LennyGodart/THE-WALL/docs/images/panel-notes.de.png

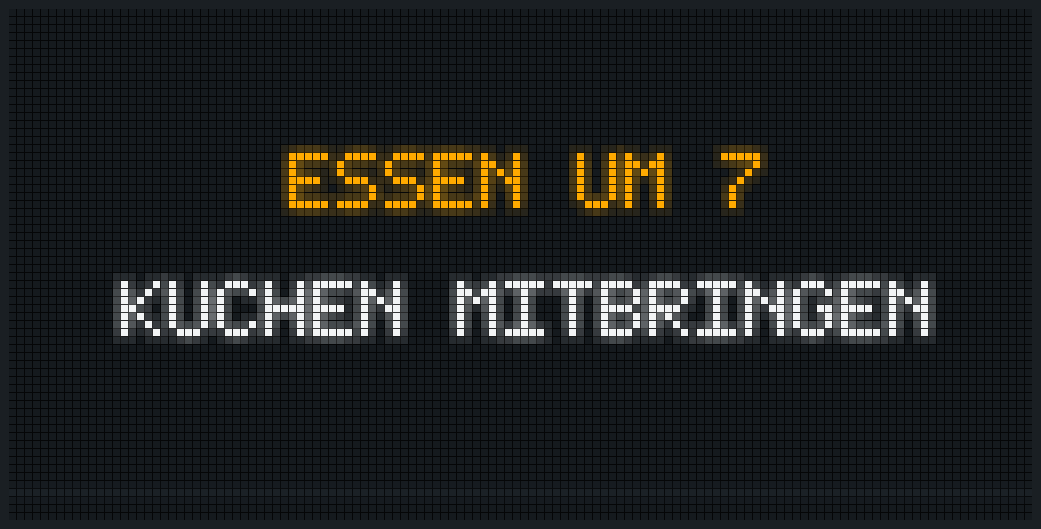
docs/images/panel-notes.de.png
