LennyGodart/THE-WALL/docs/images/site-device.de.png

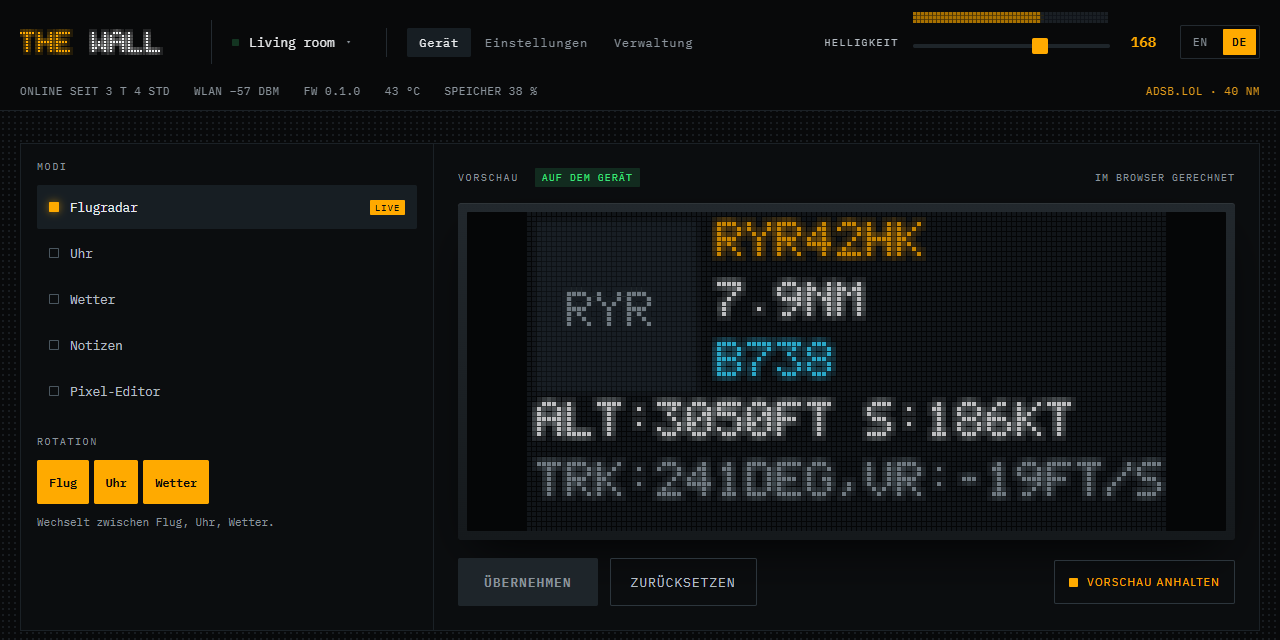
docs/images/site-device.de.png
