LennyGodart/THE-WALL/docs/images/site-flight.de.png

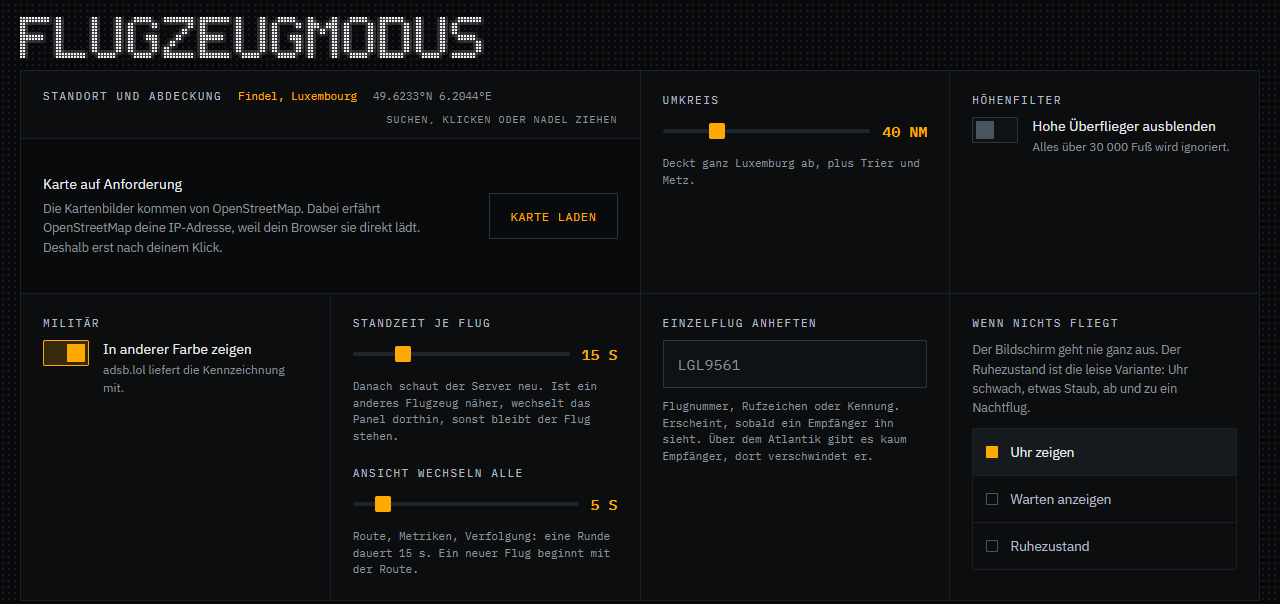
docs/images/site-flight.de.png
