LennyGodart/THE-WALL/firmware/src/certs.h

// Erzeugt von tools/certs.mjs, nicht von Hand aendern. Stammzertifikate fuer den Server.
#pragma once

static const char ROOT_CERTS[] =
// GTS Root R1
"-----BEGIN CERTIFICATE-----\n"
"MIIFVzCCAz+gAwIBAgINAgPlk28xsBNJiGuiFzANBgkqhkiG9w0BAQwFADBHMQsw\n"
"CQYDVQQGEwJVUzEiMCAGA1UEChMZR29vZ2xlIFRydXN0IFNlcnZpY2VzIExMQzEU\n"
"MBIGA1UEAxMLR1RTIFJvb3QgUjEwHhcNMTYwNjIyMDAwMDAwWhcNMzYwNjIyMDAw\n"
"MDAwWjBHMQswCQYDVQQGEwJVUzEiMCAGA1UEChMZR29vZ2xlIFRydXN0IFNlcnZp\n"
"Y2VzIExMQzEUMBIGA1UEAxMLR1RTIFJvb3QgUjEwggIiMA0GCSqGSIb3DQEBAQUA\n"
"A4ICDwAwggIKAoICAQC2EQKLHuOhd5s73L+UPreVp0A8of2C+X0yBoJx9vaMf/vo\n"
"27xqLpeXo4xL+Sv2sfnOhB2x+cWX3u+58qPpvBKJXqeqUqv4IyfLpLGcY9vXmX7w\n"
"Cl7raKb0xlpHDU0QM+NOsROjyBhsS+z8CZDfnWQpJSMHobTSPS5g4M/SCYe7zUjw\n"
"TcLCeoiKu7rPWRnWr4+wB7CeMfGCwcDfLqZtbBkOtdh+JhpFAz2weaSUKK0Pfybl\n"
"qAj+lug8aJRT7oM6iCsVlgmy4HqMLnXWnOunVmSPlk9orj2XwoSPwLxAwAtcvfaH\n"
"szVsrBhQf4TgTM2S0yDpM7xSma8ytSmzJSq0SPly4cpk9+aCEI3oncKKiPo4Zor8\n"
"Y/kB+Xj9e1x3+naH+uzfsQ55lVe0vSbv1gHR6xYKu44LtcXFilWr06zqkUspzBmk\n"
"MiVOKvFlRNACzqrOSbTqn3yDsEB750Orp2yjj32JgfpMpf/VjsPOS+C12LOORc92\n"
"wO1AK/1TD7Cn1TsNsYqiA94xrcx36m97PtbfkSIS5r762DL8EGMUUXLeXdYWk70p\n"
"aDPvOmbsB4om3xPXV2V4J95eSRQAogB/mqghtqmxlbCluQ0WEdrHbEg8QOB+DVrN\n"
"VjzRlwW5y0vtOUucxD/SVRNuJLDWcfr0wbrM7Rv1/oFB2ACYPTrIrnqYNxgFlQID\n"
"AQABo0IwQDAOBgNVHQ8BAf8EBAMCAYYwDwYDVR0TAQH/BAUwAwEB/zAdBgNVHQ4E\n"
"FgQU5K8rJnEaK0gnhS9SZizv8IkTcT4wDQYJKoZIhvcNAQEMBQADggIBAJ+qQibb\n"
"C5u+/x6Wki4+omVKapi6Ist9wTrYggoGxval3sBOh2Z5ofmmWJyq+bXmYOfg6LEe\n"
"QkEzCzc9zolwFcq1JKjPa7XSQCGYzyI0zzvFIoTgxQ6KfF2I5DUkzps+GlQebtuy\n"
"h6f88/qBVRRiClmpIgUxPoLW7ttXNLwzldMXG+gnoot7TiYaelpkttGsN/H9oPM4\n"
"7HLwEXWdyzRSjeZ2axfG34arJ45JK3VmgRAhpuo+9K4l/3wV3s6MJT/KYnAK9y8J\n"
"ZgfIPxz88NtFMN9iiMG1D53Dn0reWVlHxYciNuaCp+0KueIHoI17eko8cdLiA6Ef\n"
"MgfdG+RCzgwARWGAtQsgWSl4vflVy2PFPEz0tv/bal8xa5meLMFrUKTX5hgUvYU/\n"
"Z6tGn6D/Qqc6f1zLXbBwHSs09dR2CQzreExZBfMzQsNhFRAbd03OIozUhfJFfbdT\n"
"6u9AWpQKXCBfTkBdYiJ23//OYb2MI3jSNwLgjt7RETeJ9r/tSQdirpLsQBqvFAnZ\n"
"0E6yove+7u7Y/9waLd64NnHi/Hm3lCXRSHNboTXns5lndcEZOitHTtNCjv0xyBZm\n"
"2tIMPNuzjsmhDYAPexZ3FL//2wmUspO8IFgV6dtxQ/PeEMMA3KgqlbbC1j+Qa3bb\n"
"bP6MvPJwNQzcmRk13NfIRmPVNnGuV/u3gm3c\n"
"-----END CERTIFICATE-----\n"
// GTS Root R3
"-----BEGIN CERTIFICATE-----\n"
"MIICCTCCAY6gAwIBAgINAgPluILrIPglJ209ZjAKBggqhkjOPQQDAzBHMQswCQYD\n"
"VQQGEwJVUzEiMCAGA1UEChMZR29vZ2xlIFRydXN0IFNlcnZpY2VzIExMQzEUMBIG\n"
"A1UEAxMLR1RTIFJvb3QgUjMwHhcNMTYwNjIyMDAwMDAwWhcNMzYwNjIyMDAwMDAw\n"
"WjBHMQswCQYDVQQGEwJVUzEiMCAGA1UEChMZR29vZ2xlIFRydXN0IFNlcnZpY2Vz\n"
"IExMQzEUMBIGA1UEAxMLR1RTIFJvb3QgUjMwdjAQBgcqhkjOPQIBBgUrgQQAIgNi\n"
"AAQfTzOHMymKoYTey8chWEGJ6ladK0uFxh1MJ7x/JlFyb+Kf1qPKzEUURout736G\n"
"jOyxfi//qXGdGIRFBEFVbivqJn+7kAHjSxm65FSWRQmx1WyRRK2EE46ajA2ADDL2\n"
"4CejQjBAMA4GA1UdDwEB/wQEAwIBhjAPBgNVHRMBAf8EBTADAQH/MB0GA1UdDgQW\n"
"BBTB8Sa6oC2uhYHP0/EqEr24Cmf9vDAKBggqhkjOPQQDAwNpADBmAjEA9uEglRR7\n"
"VKOQFhG/hMjqb2sXnh5GmCCbn9MN2azTL818+FsuVbu/3ZL3pAzcMeGiAjEA/Jdm\n"
"ZuVDFhOD3cffL74UOO0BzrEXGhF16b0DjyZ+hOXJYKaV11RZt+cRLInUue4X\n"
"-----END CERTIFICATE-----\n"
// GTS Root R4
"-----BEGIN CERTIFICATE-----\n"
"MIICCTCCAY6gAwIBAgINAgPlwGjvYxqccpBQUjAKBggqhkjOPQQDAzBHMQswCQYD\n"
"VQQGEwJVUzEiMCAGA1UEChMZR29vZ2xlIFRydXN0IFNlcnZpY2VzIExMQzEUMBIG\n"
"A1UEAxMLR1RTIFJvb3QgUjQwHhcNMTYwNjIyMDAwMDAwWhcNMzYwNjIyMDAwMDAw\n"
"WjBHMQswCQYDVQQGEwJVUzEiMCAGA1UEChMZR29vZ2xlIFRydXN0IFNlcnZpY2Vz\n"
"IExMQzEUMBIGA1UEAxMLR1RTIFJvb3QgUjQwdjAQBgcqhkjOPQIBBgUrgQQAIgNi\n"
"AATzdHOnaItgrkO4NcWBMHtLSZ37wWHO5t5GvWvVYRg1rkDdc/eJkTBa6zzuhXyi\n"
"QHY7qca4R9gq55KRanPpsXI5nymfopjTX15YhmUPoYRlBtHci8nHc8iMai/lxKvR\n"
"HYqjQjBAMA4GA1UdDwEB/wQEAwIBhjAPBgNVHRMBAf8EBTADAQH/MB0GA1UdDgQW\n"
"BBSATNbrdP9JNqPV2Py1PsVq8JQdjDAKBggqhkjOPQQDAwNpADBmAjEA6ED/g94D\n"
"9J+uHXqnLrmvT/aDHQ4thQEd0dlq7A/Cr8deVl5c1RxYIigL9zC2L7F8AjEA8GE8\n"
"p/SgguMh1YQdc4acLa/KNJvxn7kjNuK8YAOdgLOaVsjh4rsUecrNIdSUtUlD\n"
"-----END CERTIFICATE-----\n"
// ISRG Root X1
"-----BEGIN CERTIFICATE-----\n"
"MIIFazCCA1OgAwIBAgIRAIIQz7DSQONZRGPgu2OCiwAwDQYJKoZIhvcNAQELBQAw\n"
"TzELMAkGA1UEBhMCVVMxKTAnBgNVBAoTIEludGVybmV0IFNlY3VyaXR5IFJlc2Vh\n"
"cmNoIEdyb3VwMRUwEwYDVQQDEwxJU1JHIFJvb3QgWDEwHhcNMTUwNjA0MTEwNDM4\n"
"WhcNMzUwNjA0MTEwNDM4WjBPMQswCQYDVQQGEwJVUzEpMCcGA1UEChMgSW50ZXJu\n"
"ZXQgU2VjdXJpdHkgUmVzZWFyY2ggR3JvdXAxFTATBgNVBAMTDElTUkcgUm9vdCBY\n"
"MTCCAiIwDQYJKoZIhvcNAQEBBQADggIPADCCAgoCggIBAK3oJHP0FDfzm54rVygc\n"
"h77ct984kIxuPOZXoHj3dcKi/vVqbvYATyjb3miGbESTtrFj/RQSa78f0uoxmyF+\n"
"0TM8ukj13Xnfs7j/EvEhmkvBioZxaUpmZmyPfjxwv60pIgbz5MDmgK7iS4+3mX6U\n"
"A5/TR5d8mUgjU+g4rk8Kb4Mu0UlXjIB0ttov0DiNewNwIRt18jA8+o+u3dpjq+sW\n"
"T8KOEUt+zwvo/7V3LvSye0rgTBIlDHCNAymg4VMk7BPZ7hm/ELNKjD+Jo2FR3qyH\n"
"B5T0Y3HsLuJvW5iB4YlcNHlsdu87kGJ55tukmi8mxdAQ4Q7e2RCOFvu396j3x+UC\n"
"B5iPNgiV5+I3lg02dZ77DnKxHZu8A/lJBdiB3QW0KtZB6awBdpUKD9jf1b0SHzUv\n"
"KBds0pjBqAlkd25HN7rOrFleaJ1/ctaJxQZBKT5ZPt0m9STJEadao0xAH0ahmbWn\n"
"OlFuhjuefXKnEgV4We0+UXgVCwOPjdAvBbI+e0ocS3MFEvzG6uBQE3xDk3SzynTn\n"
"jh8BCNAw1FtxNrQHusEwMFxIt4I7mKZ9YIqioymCzLq9gwQbooMDQaHWBfEbwrbw\n"
"qHyGO0aoSCqI3Haadr8faqU9GY/rOPNk3sgrDQoo//fb4hVC1CLQJ13hef4Y53CI\n"
"rU7m2Ys6xt0nUW7/vGT1M0NPAgMBAAGjQjBAMA4GA1UdDwEB/wQEAwIBBjAPBgNV\n"
"HRMBAf8EBTADAQH/MB0GA1UdDgQWBBR5tFnme7bl5AFzgAiIyBpY9umbbjANBgkq\n"
"hkiG9w0BAQsFAAOCAgEAVR9YqbyyqFDQDLHYGmkgJykIrGF1XIpu+ILlaS/V9lZL\n"
"ubhzEFnTIZd+50xx+7LSYK05qAvqFyFWhfFQDlnrzuBZ6brJFe+GnY+EgPbk6ZGQ\n"
"3BebYhtF8GaV0nxvwuo77x/Py9auJ/GpsMiu/X1+mvoiBOv/2X/qkSsisRcOj/KK\n"
"NFtY2PwByVS5uCbMiogziUwthDyC3+6WVwW6LLv3xLfHTjuCvjHIInNzktHCgKQ5\n"
"ORAzI4JMPJ+GslWYHb4phowim57iaztXOoJwTdwJx4nLCgdNbOhdjsnvzqvHu7Ur\n"
"TkXWStAmzOVyyghqpZXjFaH3pO3JLF+l+/+sKAIuvtd7u+Nxe5AW0wdeRlN8NwdC\n"
"jNPElpzVmbUq4JUagEiuTDkHzsxHpFKVK7q4+63SM1N95R1NbdWhscdCb+ZAJzVc\n"
"oyi3B43njTOQ5yOf+1CceWxG1bQVs5ZufpsMljq4Ui0/1lvh+wjChP4kqKOJ2qxq\n"
"4RgqsahDYVvTH9w7jXbyLeiNdd8XM2w9U/t7y0Ff/9yi0GE44Za4rF2LN9d11TPA\n"
"mRGunUHBcnWEvgJBQl9nJEiU0Zsnvgc/ubhPgXRR4Xq37Z0j4r7g1SgEEzwxA57d\n"
"emyPxgcYxn/eR44/KJ4EBs+lVDR3veyJm+kXQ99b21/+jh5Xos1AnX5iItreGCc=\n"
"-----END CERTIFICATE-----\n"
// ISRG Root X2
"-----BEGIN CERTIFICATE-----\n"
"MIICGzCCAaGgAwIBAgIQQdKd0XLq7qeAwSxs6S+HUjAKBggqhkjOPQQDAzBPMQsw\n"
"CQYDVQQGEwJVUzEpMCcGA1UEChMgSW50ZXJuZXQgU2VjdXJpdHkgUmVzZWFyY2gg\n"
"R3JvdXAxFTATBgNVBAMTDElTUkcgUm9vdCBYMjAeFw0yMDA5MDQwMDAwMDBaFw00\n"
"MDA5MTcxNjAwMDBaME8xCzAJBgNVBAYTAlVTMSkwJwYDVQQKEyBJbnRlcm5ldCBT\n"
"ZWN1cml0eSBSZXNlYXJjaCBHcm91cDEVMBMGA1UEAxMMSVNSRyBSb290IFgyMHYw\n"
"EAYHKoZIzj0CAQYFK4EEACIDYgAEzZvVn4CDCuwJSvMWSj5cz3es3mcFDR0HttwW\n"
"+1qLFNvicWDEukWVEYmO6gbf9yoWHKS5xcUy4APgHoIYOIvXRdgKam7mAHf7AlF9\n"
"ItgKbppbd9/w+kHsOdx1ymgHDB/qo0IwQDAOBgNVHQ8BAf8EBAMCAQYwDwYDVR0T\n"
"AQH/BAUwAwEB/zAdBgNVHQ4EFgQUfEKWrt5LSDv6kviejM9ti6lyN5UwCgYIKoZI\n"
"zj0EAwMDaAAwZQIwe3lORlCEwkSHRhtFcP9Ymd70/aTSVaYgLXTWNLxBo1BfASdW\n"
"tL4ndQavEi51mI38AjEAi/V3bNTIZargCyzuFJ0nN6T5U6VR5CmD1/iQMVtCnwr1\n"
"/q4AaOeMSQ+2b1tbFfLn\n"
"-----END CERTIFICATE-----\n"
// SSL.com TLS RSA Root CA 2022
"-----BEGIN CERTIFICATE-----\n"
"MIIFiTCCA3GgAwIBAgIQb77arXO9CEDii02+1PdbkTANBgkqhkiG9w0BAQsFADBO\n"
"MQswCQYDVQQGEwJVUzEYMBYGA1UECgwPU1NMIENvcnBvcmF0aW9uMSUwIwYDVQQD\n"
"DBxTU0wuY29tIFRMUyBSU0EgUm9vdCBDQSAyMDIyMB4XDTIyMDgyNTE2MzQyMloX\n"
"DTQ2MDgxOTE2MzQyMVowTjELMAkGA1UEBhMCVVMxGDAWBgNVBAoMD1NTTCBDb3Jw\n"
"b3JhdGlvbjElMCMGA1UEAwwcU1NMLmNvbSBUTFMgUlNBIFJvb3QgQ0EgMjAyMjCC\n"
"AiIwDQYJKoZIhvcNAQEBBQADggIPADCCAgoCggIBANCkCXJPQIgSYT41I57u9nTP\n"
"L3tYPc48DRAokC+X94xI2KDYJbFMsBFMF3NQ0CJKY7uB0ylu1bUJPiYYf7ISf5OY\n"
"t6/wNr/y7hienDtSxUcZXXTzZGbVXcdotL8bHAajvI9AI7YexoS9UcQbOcGV0ins\n"
"S657Lb85/bRi3pZ7QcacoOAGcvvwB5cJOYF0r/c0WRFXCsJbwST0MXMwgsadugL3\n"
"PnxEX4MN8/HdIGkWCVDi1FW24IBydm5MR7d1VVm0U3TZlMZBrViKMWYPHqIbKUBO\n"
"L9975hYsLfy/7PO0+r4Y9ptJ1O4Fbtk085zx7AGL0SDGD6C1vBdOSHtRwvzpXGk3\n"
"R2azaPgVKPC506QVzFpPulJwoxJF3ca6TvvC0PeoUidtbnm1jPx7jMEWTO6Af77w\n"
"dr5BUxIzrlo4QqvXDz5BjXYHMtWrifZOZ9mxQnUjbvPNQrL8VfVThxc7wDNY8VLS\n"
"+YCk8OjwO4s4zKTGkH8PnP2L0aPP2oOnaclQNtVcBdIKQXTbYxE3waWglksejBYS\n"
"d66UNHsef8JmAOSqg+qKkK3ONkRN0VHpvB/zagX9wHQfJRlAUW7qglFA35u5CCoG\n"
"AtUjHBPW6dvbxrB6y3snm/vg1UYk7RBLY0ulBY+6uB0rpvqR4pJSvezrZ5dtmi2f\n"
"gTIFZzL7SAg/2SW4BCUvAgMBAAGjYzBhMA8GA1UdEwEB/wQFMAMBAf8wHwYDVR0j\n"
"BBgwFoAU+y437uOEeicuzRk1sTN8/9REQrkwHQYDVR0OBBYEFPsuN+7jhHonLs0Z\n"
"NbEzfP/UREK5MA4GA1UdDwEB/wQEAwIBhjANBgkqhkiG9w0BAQsFAAOCAgEAjYlt\n"
"hEUY8U+zoO9opMAdrDC8Z2awms22qyIZZtM7QbUQnRC6cm4pJCAcAZli05bg4vsM\n"
"QtfhWsSWTVTNj8pDU/0quOr4ZcoBwq1gaAafORpR2eCNJvkLTqVTJXojpBzOCBvf\n"
"R4iyrT7gJ4eLSYwfqUdYe5byiB0YrrPRpgqU+tvT5TgKa3kSM/tKWTcWQA673vWJ\n"
"DPFs0/dRa1419dvAJuoSc06pkZCmF8NsLzjUo3KUQyxi4U5cMj29TH0ZR6LDSeeW\n"
"P4+a0zvkEdiLA9z2tmBVGKaBUfPhqBVq6+AL8BQx1rmMRTqoENjwuSfr98t67wVy\n"
"lrXEj5ZzxOhWc5y8aVFjvO9nHEMaX3cZHxj4HCUp+UmZKbaSPaKDN7EgkaibMOlq\n"
"bLQjk2UEqxHzDh1TJElTHaE/nUiSEeJ9DU/1172iWD54nR4fK/4huxoTtrEoZP2w\n"
"AgDHbICivRZQIA9ygV/MlP+7mea6kMvq+cYMwq7FGc4zoWtcu358NFcXrfA/rs3q\n"
"r5nsLFR+jM4uElZI7xc7P0peYNLcdDa8pUNjyw9bowJWCZ4kLOGGgYz+qxcs+sji\n"
"Mho6/4UIyYOf8kpIEFR3N+2ivEC+5BB09+Rbu7nzifmPQdjH5FCQNYA+HLhNkNPU\n"
"98OwoX6EyneSMSy4kLGCenROmxMmtNVQZlR4rmA=\n"
"-----END CERTIFICATE-----\n"
// SSL.com TLS ECC Root CA 2022
"-----BEGIN CERTIFICATE-----\n"
"MIICOjCCAcCgAwIBAgIQFAP1q/s3ixdAW+JDsqXRxDAKBggqhkjOPQQDAzBOMQsw\n"
"CQYDVQQGEwJVUzEYMBYGA1UECgwPU1NMIENvcnBvcmF0aW9uMSUwIwYDVQQDDBxT\n"
"U0wuY29tIFRMUyBFQ0MgUm9vdCBDQSAyMDIyMB4XDTIyMDgyNTE2MzM0OFoXDTQ2\n"
"MDgxOTE2MzM0N1owTjELMAkGA1UEBhMCVVMxGDAWBgNVBAoMD1NTTCBDb3Jwb3Jh\n"
"dGlvbjElMCMGA1UEAwwcU1NMLmNvbSBUTFMgRUNDIFJvb3QgQ0EgMjAyMjB2MBAG\n"
"ByqGSM49AgEGBSuBBAAiA2IABEUpNXP6wrgjzhR9qLFNoFs27iosU8NgCTWyJGYm\n"
"acCzldZdkkAZDsalE3D07xJRKF3nzL35PIXBz5SQySvOkkJYWWf9lCcQZIxPBLFN\n"
"SeR7T5v15wj4A4j3p8OSSxlUgaNjMGEwDwYDVR0TAQH/BAUwAwEB/zAfBgNVHSME\n"
"GDAWgBSJjy+j6CugFFR781a4Jl9nOAuc0DAdBgNVHQ4EFgQUiY8vo+groBRUe/NW\n"
"uCZfZzgLnNAwDgYDVR0PAQH/BAQDAgGGMAoGCCqGSM49BAMDA2gAMGUCMFXjIlbp\n"
"15IkWE8elDIPDAI2wv2sdDJO4fscgIijzPvX6yv/N33w7deedWo1dlJF4AIxAMeN\n"
"b0Igj762TVntd00pxCAgRWSGOlDGxK0tk/UYfXLtqc/ErFc2KAhl3zx5Zn6g6g==\n"
"-----END CERTIFICATE-----\n"
// SSL.com Root Certification Authority RSA
"-----BEGIN CERTIFICATE-----\n"
"MIIF3TCCA8WgAwIBAgIIeyyb0xaAMpkwDQYJKoZIhvcNAQELBQAwfDELMAkGA1UE\n"
"BhMCVVMxDjAMBgNVBAgMBVRleGFzMRAwDgYDVQQHDAdIb3VzdG9uMRgwFgYDVQQK\n"
"DA9TU0wgQ29ycG9yYXRpb24xMTAvBgNVBAMMKFNTTC5jb20gUm9vdCBDZXJ0aWZp\n"
"Y2F0aW9uIEF1dGhvcml0eSBSU0EwHhcNMTYwMjEyMTczOTM5WhcNNDEwMjEyMTcz\n"
"OTM5WjB8MQswCQYDVQQGEwJVUzEOMAwGA1UECAwFVGV4YXMxEDAOBgNVBAcMB0hv\n"
"dXN0b24xGDAWBgNVBAoMD1NTTCBDb3Jwb3JhdGlvbjExMC8GA1UEAwwoU1NMLmNv\n"
"bSBSb290IENlcnRpZmljYXRpb24gQXV0aG9yaXR5IFJTQTCCAiIwDQYJKoZIhvcN\n"
"AQEBBQADggIPADCCAgoCggIBAPkP3aMrfcvQKv7sZ4Wm5y4bunfh4/WvpOz6Sl2R\n"
"xFdHaxh3a3by/ZPkPQ/CFp4LZsNWlJ4Xg4XOVu/yFv0AYvUiCVToZRdOQbngT0aX\n"
"qhvIuG5iXmmxX9sqAn78bMrzQdjt0Oj8P2FI7bADFB0QDksZ4LtO7IZl/zbzXmcC\n"
"C52GVWH9ejjt/uIZALdvoVBidXQ8oPrIJZK0bnoix/geoeOy3ZExqysdBP+lSgQ3\n"
"6YWkMyv94tZVNHwZpEpox7Ko07fKoZOI68GXvIz5HdkihCR0xwQ9aqkpk8zruFvh\n"
"/l8lqjRYyMEjVJ0bmBHDOJx+PYZspQ9AhnwC9FwCTyjLrnGfDzrIM/4RJTXq/LrF\n"
"YD3ZfBjVsqnTdXgDciLKOsMf7yzlLqn6niy2UUb9rwPW6mBo6oUWNmuF6R7As93E\n"
"JNyAKoFBbZQ+yODJgUEAnl6/f8UImKIYLEJAs/lvOCdLToD0PYFH4Ih86hzOtXVc\n"
"US4cK38acijnALXRdMbX5J+tB5O2UzU1/Dfkw/ZdFr4hc96SCvigY2q8lpJqPvi8\n"
"ZVWb3vUNiSYE/CUapiVpy8JtynziWV+XrOvvLsi81xtZPCvM8hnIk2snYxnP/Okm\n"
"+Mpxm3+T/jRnhE6Z6/yzeAkzcLpmpnbtG3PrGqUNxCITIJRWCk4sbE6x/c+cCbqi\n"
"M+2HAgMBAAGjYzBhMB0GA1UdDgQWBBTdBAkHovV6fVJTEpKV7jiAJQ2mWTAPBgNV\n"
"HRMBAf8EBTADAQH/MB8GA1UdIwQYMBaAFN0ECQei9Xp9UlMSkpXuOIAlDaZZMA4G\n"
"A1UdDwEB/wQEAwIBhjANBgkqhkiG9w0BAQsFAAOCAgEAIBgRlCn7Jp0cHh5wYfGV\n"
"cpNxJK1ok1iOMq8bs3AD/CUrdIWQPXhq9LmLpZc7tRiRux6n+UBbkflVma8eEdBc\n"
"Hadm47GUBwwyOabqG7B52B2ccETjit3E+ZUfijhDPwGFpUenPUayvOUiaPd7nNgs\n"
"PgohyC0zrL/FgZkxdMF1ccW+sfAjRfSda/wZY52jvATGGAslu1OJD7OAUN5F7kR/\n"
"q5R4ZJjT9ijdh9hwZXT7DrkT66cPYakylszeu+1jTBi7qUD3oFRuIIhxdRjqerQ0\n"
"cuAjJ3dctpDqhiVAq+8zD8ufgr6iIPv2tS0a5sKFsXQP+8hlAqRSAUfdSSLBv9jr\n"
"a6x+3uxjMxW3IwiPxg+NQVrdjsW5j+VFP3jbutIbQLH+cU0/4IGiul607BXgk90I\n"
"H37hVZkLId6Tngr75qNJvTYw/ud3sqB1l7UtgYgXZSD32pAAn8lSzDLKNXz1PQ/Y\n"
"K9f1JmzJBjSWFupwWRoyeXkLtoh/D1JIPb9s2KJELtFOt3JY04kTlf5Eq/jXixtu\n"
"nLwsoFvVagCvXzfh1foQC5ichucmj87w7G6KVwuA406ywKBjYZC6VWg3dGq2ktuf\n"
"oYYitmUnDuy2n0Jg5GfCtdpBC8TTi2EbvPofkSvXRAdeuims2cXp71NIWuuA8ShY\n"
"Ic2wBlX7Jz9TkHCpBB5XJ7k=\n"
"-----END CERTIFICATE-----\n"
// SSL.com Root Certification Authority ECC
"-----BEGIN CERTIFICATE-----\n"
"MIICjTCCAhSgAwIBAgIIdebfy8FoW6gwCgYIKoZIzj0EAwIwfDELMAkGA1UEBhMC\n"
"VVMxDjAMBgNVBAgMBVRleGFzMRAwDgYDVQQHDAdIb3VzdG9uMRgwFgYDVQQKDA9T\n"
"U0wgQ29ycG9yYXRpb24xMTAvBgNVBAMMKFNTTC5jb20gUm9vdCBDZXJ0aWZpY2F0\n"
"aW9uIEF1dGhvcml0eSBFQ0MwHhcNMTYwMjEyMTgxNDAzWhcNNDEwMjEyMTgxNDAz\n"
"WjB8MQswCQYDVQQGEwJVUzEOMAwGA1UECAwFVGV4YXMxEDAOBgNVBAcMB0hvdXN0\n"
"b24xGDAWBgNVBAoMD1NTTCBDb3Jwb3JhdGlvbjExMC8GA1UEAwwoU1NMLmNvbSBS\n"
"b290IENlcnRpZmljYXRpb24gQXV0aG9yaXR5IEVDQzB2MBAGByqGSM49AgEGBSuB\n"
"BAAiA2IABEVuqVDEpiM2nl8ojRfLliJkP9x6jh3MCLOicSS6jkm5BBtHllirLZXI\n"
"7Z4INcgn64mMU1jrYor+8FsPazFSY0E7ic3s7LaNGdM0B9y7xgZ/wkWV7Mt/qCPg\n"
"CemB+vNH06NjMGEwHQYDVR0OBBYEFILRhXMw5zUE044CkvvlpNHEIejNMA8GA1Ud\n"
"EwEB/wQFMAMBAf8wHwYDVR0jBBgwFoAUgtGFczDnNQTTjgKS++Wk0cQh6M0wDgYD\n"
"VR0PAQH/BAQDAgGGMAoGCCqGSM49BAMCA2cAMGQCMG/n61kRpGDPYbCWe+0F+S8T\n"
"kdzt5fxQaxFGRrMcIQBiu77D5+jNB5n5DQtdcj7EqgIwH7y6C+IwJPt8bYBVCpk+\n"
"gA0z5Wajs6O7pdWLjwkspl1+4vAHCGht0nxpbl/f5Wpl\n"
"-----END CERTIFICATE-----\n"
// GlobalSign Root R46
"-----BEGIN CERTIFICATE-----\n"
"MIIFWjCCA0KgAwIBAgISEdK7udcjGJ5AXwqdLdDfJWfRMA0GCSqGSIb3DQEBDAUA\n"
"MEYxCzAJBgNVBAYTAkJFMRkwFwYDVQQKExBHbG9iYWxTaWduIG52LXNhMRwwGgYD\n"
"VQQDExNHbG9iYWxTaWduIFJvb3QgUjQ2MB4XDTE5MDMyMDAwMDAwMFoXDTQ2MDMy\n"
"MDAwMDAwMFowRjELMAkGA1UEBhMCQkUxGTAXBgNVBAoTEEdsb2JhbFNpZ24gbnYt\n"
"c2ExHDAaBgNVBAMTE0dsb2JhbFNpZ24gUm9vdCBSNDYwggIiMA0GCSqGSIb3DQEB\n"
"AQUAA4ICDwAwggIKAoICAQCsrHQy6LNl5brtQyYdpokNRbopiLKkHWPd08EsCVeJ\n"
"OaFV6Wc0dwxu5FUdUiXSE2te4R2pt32JMl8Nnp8semNgQB+msLZ4j5lUlghYruQG\n"
"vGIFAha/r6gjA7aUD7xubMLL1aa7DOn2wQL7Id5m3RerdELv8HQvJfTqa1VbkNud\n"
"316HCkD7rRlr+/fKYIje2sGP1q7Vf9Q8g+7XFkyDRTNrJ9CG0Bwta/OrffGFqfUo\n"
"0q3v84RLHIf8E6M6cqJaESvWJ3En7YEtbWaBkoe0G1h6zD8K+kZPTXhc+CtI4wSE\n"
"y132tGqzZfxCnlEmIyDLPRT5ge1lFgBPGmSXZgjPjHvjK8Cd+RTyG/FWaha/LIWF\n"
"zXg4mutCagI0GIMXTpRW+LaCtfOW3T3zvn8gdz57GSNrLNRyc0NXfeD412lPFzYE\n"
"+cCQYDdF3uYM2HSNrpyibXRdQr4G9dlkbgIQrImwTDsHTUB+JMWKmIJ5jqSngiCN\n"
"I/onccnfxkF0oE32kRbcRoxfKWMxWXEM2G/CtjJ9++ZdU6Z+Ffy7dXxd7Pj2Fxzs\n"
"x2sZy/N78CsHpdlseVR2bJ0cpm4O6XkMqCNqo98bMDGfsVR7/mrLZqrcZdCinkqa\n"
"ByFrgY/bxFn63iLABJzjqls2k+g9vXqhnQt2sQvHnf3PmKgGwvgqo6GDoLclcqUC\n"
"4wIDAQABo0IwQDAOBgNVHQ8BAf8EBAMCAYYwDwYDVR0TAQH/BAUwAwEB/zAdBgNV\n"
"HQ4EFgQUA1yrc4GHqMywptWU4jaWSf8FmSwwDQYJKoZIhvcNAQEMBQADggIBAHx4\n"
"7PYCLLtbfpIrXTncvtgdokIzTfnvpCo7RGkerNlFo048p9gkUbJUHJNOxO97k4Vg\n"
"JuoJSOD1u8fpaNK7ajFxzHmuEajwmf3lH7wvqMxX63bEIaZHU1VNaL8FpO7XJqti\n"
"2kM3S+LGteWygxk6x9PbTZ4IevPuzz5i+6zoYMzRx6Fcg0XERczzF2sUyQQCPtIk\n"
"pnnpHs6i58FZFZ8d4kuaPp92CC1r2LpXFNqD6v6MVenQTqnMdzGxRBF6XLE+0xRF\n"
"FRhiJBPSy03OXIPBNvIQtQ6IbbjhVp+J3pZmOUdkLG5NrmJ7v2B0GbhWrJKsFjLt\n"
"rWhV/pi60zTe9Mlhww6G9kuEYO4Ne7UyWHmRVSyBQ7N0H3qqJZ4d16GLuc1CLgSk\n"
"ZoNNiTW2bKg2SnkheCLQQrzRQDGQob4Ez8pn7fXwgNNgyYMqIgXQBztSvwyeqiv5\n"
"u+YfjyW6hY0XHgL+XVAEV8/+LbzvXMAaq7afJMbfc2hIkCwU9D9SGuTSyxTDYWnP\n"
"4vkYxboznxSjBF25cfe1lNj2M8FawTSLfJvdkzrnE6JwYZ+vj+vYxXX4M2bUdGc6\n"
"N3ec592kD3ZDZopD8p/7DEJ4Y9HiD2971KE9dJeFt0g5QdYg/NA6s/rob8SKunE3\n"
"vouXsXgxT7PntgMTzlSdriVZzH81Xwj3QEUxeCp6\n"
"-----END CERTIFICATE-----\n"
// GlobalSign Root E46
"-----BEGIN CERTIFICATE-----\n"
"MIICCzCCAZGgAwIBAgISEdK7ujNu1LzmJGjFDYQdmOhDMAoGCCqGSM49BAMDMEYx\n"
"CzAJBgNVBAYTAkJFMRkwFwYDVQQKExBHbG9iYWxTaWduIG52LXNhMRwwGgYDVQQD\n"
"ExNHbG9iYWxTaWduIFJvb3QgRTQ2MB4XDTE5MDMyMDAwMDAwMFoXDTQ2MDMyMDAw\n"
"MDAwMFowRjELMAkGA1UEBhMCQkUxGTAXBgNVBAoTEEdsb2JhbFNpZ24gbnYtc2Ex\n"
"HDAaBgNVBAMTE0dsb2JhbFNpZ24gUm9vdCBFNDYwdjAQBgcqhkjOPQIBBgUrgQQA\n"
"IgNiAAScDrHPt+ieUnd1NPqlRqetMhkytAepJ8qUuwzSChDH2omwlwxwEwkBjtjq\n"
"R+q+soArzfwoDdusvKSGN+1wCAB16pMLey5SnCNoIwZD7JIvU4Tb+0cUB+hflGdd\n"
"yXqBPCCjQjBAMA4GA1UdDwEB/wQEAwIBhjAPBgNVHRMBAf8EBTADAQH/MB0GA1Ud\n"
"DgQWBBQxCpCPtsad0kRLgLWi5h+xEk8blTAKBggqhkjOPQQDAwNoADBlAjEA31SQ\n"
"7Zvvi5QCkxeCmb6zniz2C5GMn0oUsfZkvLtoURMMA/cVi4RguYv/Uo7njLwcAjA8\n"
"+RHUjE7AwWHCFUyqqx0LMV87HOIAl0Qx5v5zli/altP+CAezNIm8BZ/3Hobui3A=\n"
"-----END CERTIFICATE-----\n"
// DigiCert Global Root G2
"-----BEGIN CERTIFICATE-----\n"
"MIIDjjCCAnagAwIBAgIQAzrx5qcRqaC7KGSxHQn65TANBgkqhkiG9w0BAQsFADBh\n"
"MQswCQYDVQQGEwJVUzEVMBMGA1UEChMMRGlnaUNlcnQgSW5jMRkwFwYDVQQLExB3\n"
"d3cuZGlnaWNlcnQuY29tMSAwHgYDVQQDExdEaWdpQ2VydCBHbG9iYWwgUm9vdCBH\n"
"MjAeFw0xMzA4MDExMjAwMDBaFw0zODAxMTUxMjAwMDBaMGExCzAJBgNVBAYTAlVT\n"
"MRUwEwYDVQQKEwxEaWdpQ2VydCBJbmMxGTAXBgNVBAsTEHd3dy5kaWdpY2VydC5j\n"
"b20xIDAeBgNVBAMTF0RpZ2lDZXJ0IEdsb2JhbCBSb290IEcyMIIBIjANBgkqhkiG\n"
"9w0BAQEFAAOCAQ8AMIIBCgKCAQEAuzfNNNx7a8myaJCtSnX/RrohCgiN9RlUyfuI\n"
"2/Ou8jqJkTx65qsGGmvPrC3oXgkkRLpimn7Wo6h+4FR1IAWsULecYxpsMNzaHxmx\n"
"1x7e/dfgy5SDN67sH0NO3Xss0r0upS/kqbitOtSZpLYl6ZtrAGCSYP9PIUkY92eQ\n"
"q2EGnI/yuum06ZIya7XzV+hdG82MHauVBJVJ8zUtluNJbd134/tJS7SsVQepj5Wz\n"
"tCO7TG1F8PapspUwtP1MVYwnSlcUfIKdzXOS0xZKBgyMUNGPHgm+F6HmIcr9g+UQ\n"
"vIOlCsRnKPZzFBQ9RnbDhxSJITRNrw9FDKZJobq7nMWxM4MphQIDAQABo0IwQDAP\n"
"BgNVHRMBAf8EBTADAQH/MA4GA1UdDwEB/wQEAwIBhjAdBgNVHQ4EFgQUTiJUIBiV\n"
"5uNu5g/6+rkS7QYXjzkwDQYJKoZIhvcNAQELBQADggEBAGBnKJRvDkhj6zHd6mcY\n"
"1Yl9PMWLSn/pvtsrF9+wX3N3KjITOYFnQoQj8kVnNeyIv/iPsGEMNKSuIEyExtv4\n"
"NeF22d+mQrvHRAiGfzZ0JFrabA0UWTW98kndth/Jsw1HKj2ZL7tcu7XUIOGZX1NG\n"
"Fdtom/DzMNU+MeKNhJ7jitralj41E6Vf8PlwUHBHQRFXGU7Aj64GxJUTFy8bJZ91\n"
"8rGOmaFvE7FBcf6IKshPECBV1/MUReXgRPTqh5Uykw7+U0b6LJ3/iyK5S9kJRaTe\n"
"pLiaWN0bfVKfjllDiIGknibVb63dDcY3fe0Dkhvld1927jyNxF1WW6LZZm6zNTfl\n"
"MrY=\n"
"-----END CERTIFICATE-----\n"
// USERTrust RSA Certification Authority
"-----BEGIN CERTIFICATE-----\n"
"MIIF3jCCA8agAwIBAgIQAf1tMPyjylGoG7xkDjUDLTANBgkqhkiG9w0BAQwFADCB\n"
"iDELMAkGA1UEBhMCVVMxEzARBgNVBAgTCk5ldyBKZXJzZXkxFDASBgNVBAcTC0pl\n"
"cnNleSBDaXR5MR4wHAYDVQQKExVUaGUgVVNFUlRSVVNUIE5ldHdvcmsxLjAsBgNV\n"
"BAMTJVVTRVJUcnVzdCBSU0EgQ2VydGlmaWNhdGlvbiBBdXRob3JpdHkwHhcNMTAw\n"
"MjAxMDAwMDAwWhcNMzgwMTE4MjM1OTU5WjCBiDELMAkGA1UEBhMCVVMxEzARBgNV\n"
"BAgTCk5ldyBKZXJzZXkxFDASBgNVBAcTC0plcnNleSBDaXR5MR4wHAYDVQQKExVU\n"
"aGUgVVNFUlRSVVNUIE5ldHdvcmsxLjAsBgNVBAMTJVVTRVJUcnVzdCBSU0EgQ2Vy\n"
"dGlmaWNhdGlvbiBBdXRob3JpdHkwggIiMA0GCSqGSIb3DQEBAQUAA4ICDwAwggIK\n"
"AoICAQCAEmUXNg7D2wiz0KxXDXbtzSfTTK1Qg2HiqiBNCS1kCdzOiZ/MPans9s/B\n"
"3PHTsdZ7NygRK0faOca8Ohm0X6a9fZ2jY0K2dvKpOyuR+OJv0OwWIJAJPuLodMkY\n"
"tJHUYmTbf6MG8YgYapAiPLz+E/CHFHv25B+O1ORRxhFnRghRy4YUVD+8M/5+bJz/\n"
"Fp0YvVGONaanZshyZ9shZrHUm3gDwFA66Mzw3LyeTP6vBZY1H1dat//O+T23LLb2\n"
"VN3I5xI6Ta5MirdcmrS3ID3KfyI0rn47aGYBROcBTkZTmzNg95S+UzeQc0PzMsNT\n"
"79uq/nROacdrjGCT3sTHDN/hMq7MkztReJVni+49Vv4M0GkPGw/zJSZrM233bkf6\n"
"c0Plfg6lZrEpfDKEY1WJxA3Bk1QwGROs0303p+tdOmw1XNtB1xLaqUkL39iAigmT\n"
"Yo61Zs8liM2EuLE/pDkP2QKe6xJMlXzzawWpXhaDzLhn4ugTncxbgtNMs+1b/97l\n"
"c6wjOy0AvzVVdAlJ2ElYGn+SNuZRkg7zJn0cTRe8yexDJtC/QV9AqURE9JnnV4ee\n"
"UB9XVKg+/XRjL7FQZQnmWEIuQxpMtPAlR1n6BB6T1CZGSlCBst6+eLf8ZxXhyVeE\n"
"Hg9j1uliutZfVS7qXMYoCAQlObgOK6nyTJccBz8NUvXt7y+CDwIDAQABo0IwQDAd\n"
"BgNVHQ4EFgQUU3m/WqorSs9UgOHYm8Cd8rIDZsswDgYDVR0PAQH/BAQDAgEGMA8G\n"
"A1UdEwEB/wQFMAMBAf8wDQYJKoZIhvcNAQEMBQADggIBAFzUfA3P9wF9QZllDHPF\n"
"Up/L+M+ZBn8b2kMVn54CVVeWFPFSPCeHlCjtHzoBN6J2/FNQwISbxmtOuowhT6KO\n"
"VWKR82kV2LyI48SqC/3vqOlLVSoGIG1VeCkZ7l8wXEskEVX/JJpuXior7gtNn3/3\n"
"ATiUFJVDBwn7YKnuHKsSjKCaXqeYalltiz8I+8jRRa8YFWSQEg9zKC7F4iRO/Fjs\n"
"8PRF/iKz6y+O0tlFYQXBl2+odnKPi4w2r78NBc5xjeambx9spnFixdjQg3IM8WcR\n"
"iQycE0xyNN+81XHfqnHd4blsjDwSXWXavVcStkNr/+XeTWYRUc+ZruwXtuhxkYze\n"
"Sf7dNXGiFSeUHM9h4ya7b6NnJSFd5t0dCy5oGzuCr+yDZ4XUmFF0sbmZgIn/f3gZ\n"
"XHlKYC6SQK5MNyosycdiyA5d9zZbyuAlJQG03RoHnHcAP9Dc1ew91Pq7P8yF1m9/\n"
"qS3fuQL39ZeatTXaw2ewh0qpKJ4jjv9cJ2vhsE/zB+4ALtRZh8tSQZXq9EfX7mRB\n"
"VXyNWQKV3WKdwrnuWih0hKWbt5DHDAff9Yk2dDLWKMGwsAvgnEzDHNb842m1R0aB\n"
"L6KCq9NjRHDEjf8tM7qtj3u1cIiuPhnPQCjY/MiQu12ZIvVS5ljFH4gxQ+6IHdfG\n"
"jjxDah2nGN59PRbxYvnKkKj9\n"
"-----END CERTIFICATE-----\n"
// USERTrust ECC Certification Authority
"-----BEGIN CERTIFICATE-----\n"
"MIICjzCCAhWgAwIBAgIQXIuZxVqUxdJxVt7NiYDMJjAKBggqhkjOPQQDAzCBiDEL\n"
"MAkGA1UEBhMCVVMxEzARBgNVBAgTCk5ldyBKZXJzZXkxFDASBgNVBAcTC0plcnNl\n"
"eSBDaXR5MR4wHAYDVQQKExVUaGUgVVNFUlRSVVNUIE5ldHdvcmsxLjAsBgNVBAMT\n"
"JVVTRVJUcnVzdCBFQ0MgQ2VydGlmaWNhdGlvbiBBdXRob3JpdHkwHhcNMTAwMjAx\n"
"MDAwMDAwWhcNMzgwMTE4MjM1OTU5WjCBiDELMAkGA1UEBhMCVVMxEzARBgNVBAgT\n"
"Ck5ldyBKZXJzZXkxFDASBgNVBAcTC0plcnNleSBDaXR5MR4wHAYDVQQKExVUaGUg\n"
"VVNFUlRSVVNUIE5ldHdvcmsxLjAsBgNVBAMTJVVTRVJUcnVzdCBFQ0MgQ2VydGlm\n"
"aWNhdGlvbiBBdXRob3JpdHkwdjAQBgcqhkjOPQIBBgUrgQQAIgNiAAQarFRaqflo\n"
"I+d61SRvU8Za2EurxtW20eZzca7dnNYMYf3boIkDuAUU7FfO7l0/4iGzzvfUinng\n"
"o4N+LZfQYcTxmdwlkWOrfzCjtHDix6EznPO/LlxTsV+zfTJ/ijTjeXmjQjBAMB0G\n"
"A1UdDgQWBBQ64QmG1M8ZwpZ2dEl23OA1xmNjmjAOBgNVHQ8BAf8EBAMCAQYwDwYD\n"
"VR0TAQH/BAUwAwEB/zAKBggqhkjOPQQDAwNoADBlAjA2Z6EWCNzklwBBHU6+4WMB\n"
"zzuqQhFkoJ2UOQIReVx7Hfpkue4WQrO/isIJxOzksU0CMQDpKmFHjFJKS04YcPbW\n"
"RNZu9YO6bVi9JNlWSOrvxKJGgYhqOkbRqZtNyWHa0V1Xahg=\n"
"-----END CERTIFICATE-----\n";
