LennyGodart/THE-WALL/firmware/src/glyphs.h

// Erzeugt von tools/font.mjs aus web/assets/js/lib/pixelfont.js, nicht von Hand aendern.
// Jede Glyphe hat 7 Zeilen zu je 5 Bits, Bit 4 ist die linke Spalte.
#pragma once
#include <cstdint>

struct Glyph {
  uint16_t cp;
  uint8_t rows[7];
};

// Nach Codepunkt sortiert, gesucht wird binaer.
static const Glyph GLYPHS[] = {
    {0x0020, {0x00, 0x00, 0x00, 0x00, 0x00, 0x00, 0x00}},
    {0x0021, {0x04, 0x04, 0x04, 0x04, 0x04, 0x00, 0x04}},
    {0x0022, {0x0A, 0x0A, 0x00, 0x00, 0x00, 0x00, 0x00}},
    {0x0023, {0x0A, 0x1F, 0x0A, 0x0A, 0x1F, 0x0A, 0x00}},
    {0x0024, {0x04, 0x0F, 0x14, 0x0E, 0x05, 0x1E, 0x04}},
    {0x0025, {0x11, 0x02, 0x04, 0x04, 0x08, 0x11, 0x00}},
    {0x0026, {0x0C, 0x12, 0x14, 0x08, 0x15, 0x12, 0x0D}},
    {0x0027, {0x04, 0x04, 0x00, 0x00, 0x00, 0x00, 0x00}},
    {0x0028, {0x02, 0x04, 0x08, 0x08, 0x08, 0x04, 0x02}},
    {0x0029, {0x08, 0x04, 0x02, 0x02, 0x02, 0x04, 0x08}},
    {0x002A, {0x00, 0x0A, 0x04, 0x0E, 0x04, 0x0A, 0x00}},
    {0x002B, {0x00, 0x04, 0x04, 0x1F, 0x04, 0x04, 0x00}},
    {0x002C, {0x00, 0x00, 0x00, 0x00, 0x04, 0x04, 0x08}},
    {0x002D, {0x00, 0x00, 0x00, 0x0E, 0x00, 0x00, 0x00}},
    {0x002E, {0x00, 0x00, 0x00, 0x00, 0x00, 0x04, 0x00}},
    {0x002F, {0x01, 0x01, 0x02, 0x04, 0x08, 0x10, 0x10}},
    {0x0030, {0x0E, 0x11, 0x13, 0x15, 0x19, 0x11, 0x0E}},
    {0x0031, {0x04, 0x0C, 0x04, 0x04, 0x04, 0x04, 0x0E}},
    {0x0032, {0x0E, 0x11, 0x01, 0x02, 0x04, 0x08, 0x1F}},
    {0x0033, {0x1F, 0x02, 0x04, 0x02, 0x01, 0x11, 0x0E}},
    {0x0034, {0x02, 0x06, 0x0A, 0x12, 0x1F, 0x02, 0x02}},
    {0x0035, {0x1F, 0x10, 0x1E, 0x01, 0x01, 0x11, 0x0E}},
    {0x0036, {0x06, 0x08, 0x10, 0x1E, 0x11, 0x11, 0x0E}},
    {0x0037, {0x1F, 0x01, 0x02, 0x04, 0x08, 0x08, 0x08}},
    {0x0038, {0x0E, 0x11, 0x11, 0x0E, 0x11, 0x11, 0x0E}},
    {0x0039, {0x0E, 0x11, 0x11, 0x0F, 0x01, 0x02, 0x0C}},
    {0x003A, {0x00, 0x04, 0x00, 0x00, 0x04, 0x00, 0x00}},
    {0x003B, {0x00, 0x04, 0x00, 0x00, 0x04, 0x04, 0x08}},
    {0x003C, {0x00, 0x02, 0x04, 0x08, 0x04, 0x02, 0x00}},
    {0x003D, {0x00, 0x00, 0x1F, 0x00, 0x1F, 0x00, 0x00}},
    {0x003E, {0x00, 0x08, 0x04, 0x02, 0x04, 0x08, 0x00}},
    {0x003F, {0x0E, 0x11, 0x01, 0x06, 0x04, 0x00, 0x04}},
    {0x0040, {0x0E, 0x11, 0x17, 0x15, 0x17, 0x10, 0x0E}},
    {0x0041, {0x0E, 0x11, 0x11, 0x1F, 0x11, 0x11, 0x11}},
    {0x0042, {0x1E, 0x11, 0x11, 0x1E, 0x11, 0x11, 0x1E}},
    {0x0043, {0x0E, 0x11, 0x10, 0x10, 0x10, 0x11, 0x0E}},
    {0x0044, {0x1E, 0x11, 0x11, 0x11, 0x11, 0x11, 0x1E}},
    {0x0045, {0x1F, 0x10, 0x10, 0x1E, 0x10, 0x10, 0x1F}},
    {0x0046, {0x1F, 0x10, 0x10, 0x1E, 0x10, 0x10, 0x10}},
    {0x0047, {0x0E, 0x11, 0x10, 0x13, 0x11, 0x11, 0x0E}},
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
};

static constexpr int GLYPH_COUNT = 101;
